Obbiwan22/Projet-cockpit_G1000_Baron_58/img/Droite.jpg

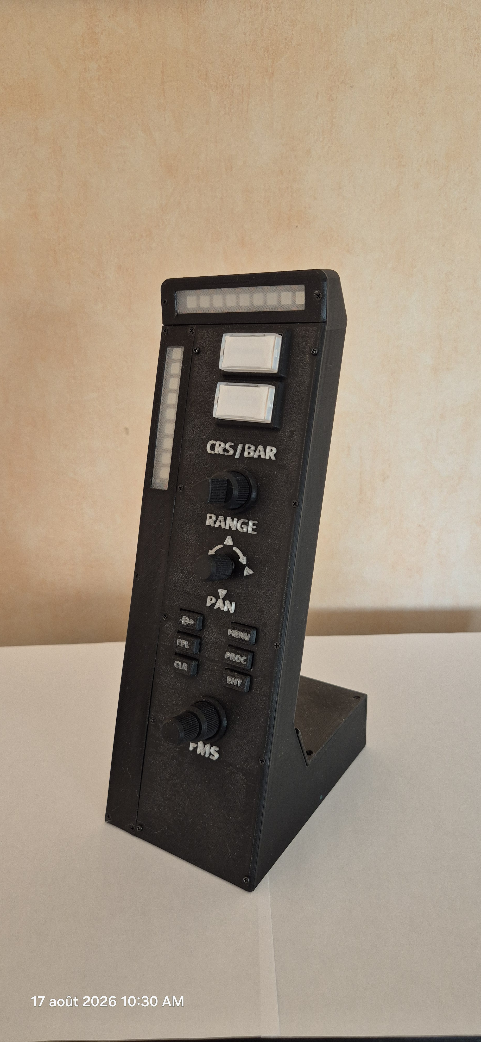
img/Droite.jpg
