Obbiwan22/Projet-cockpit_G1000_Baron_58/img/Platine Bouton sound Arriere.png

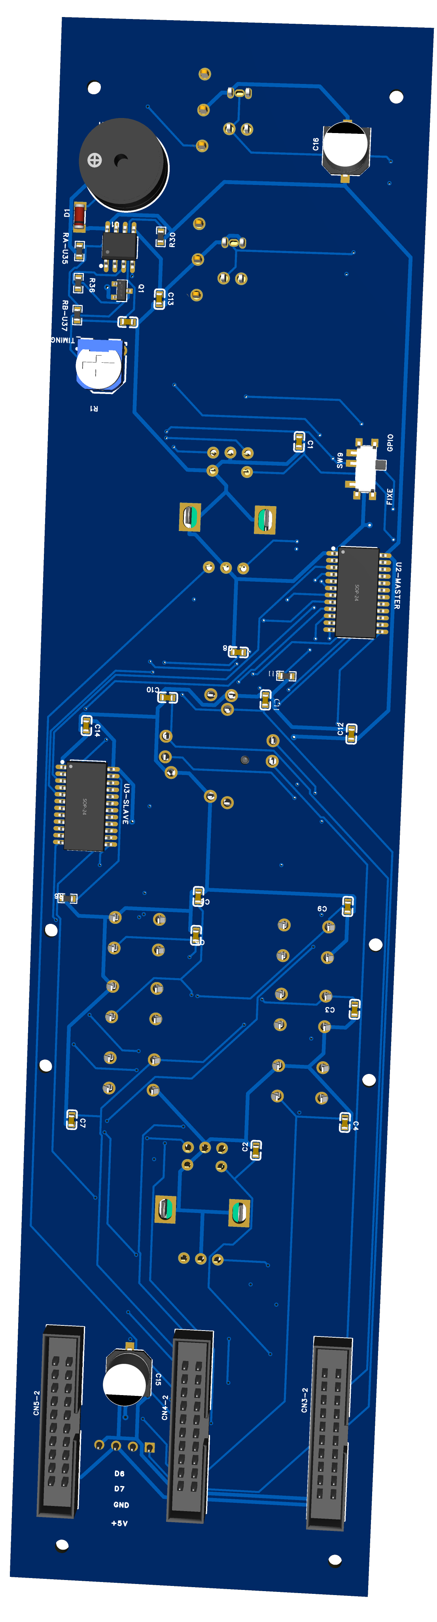
img/Platine Bouton sound Arriere.png
