Obbiwan22/Projet-cockpit_G1000_Baron_58/3D-Printing/plaque avant V3.42.STL

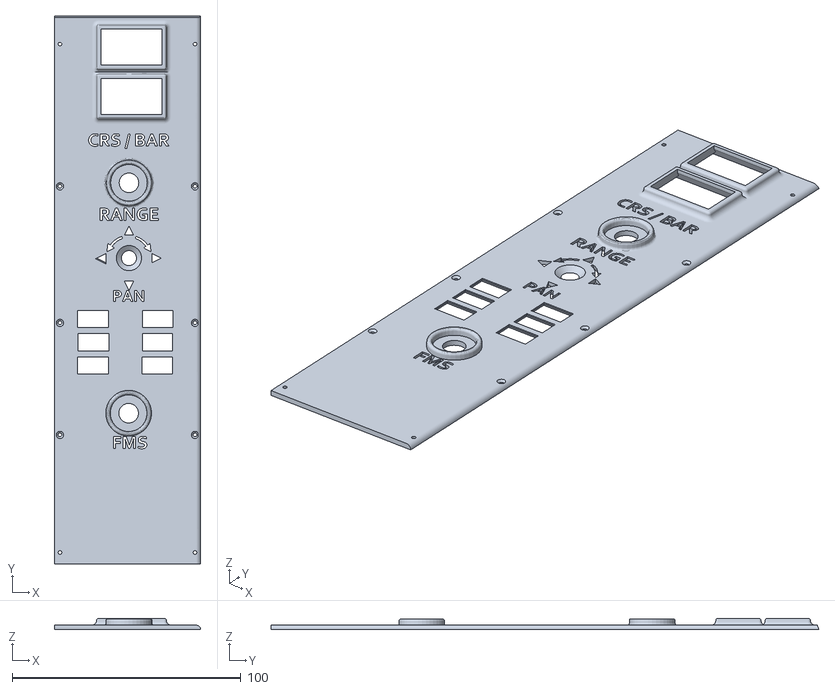
[picture p23: CAD file, 2026-08-17]
3D-Printing/plaque avant V3.42.STL
64.0 x 239.4 x 5.00
