Obbiwan22/Projet-cockpit_G1000_Baron_58/3D-Printing/plaque avant lettre V3.2.STL

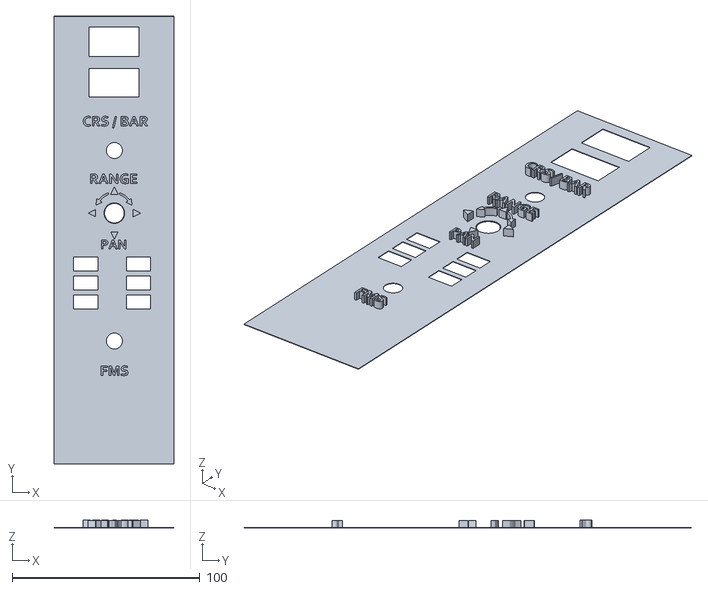
[picture p24: CAD file, 2026-08-17]
3D-Printing/plaque avant lettre V3.2.STL
64.0 x 238.8 x 4.25
