Obbiwan22/Projet-cockpit_G1000_Baron_58/firmware/ILS_NeoPixel_mega/MFCustomDevice.h

#pragma once

#include <Arduino.h>
#include "ILS_NeoPixel_mega.h"

// only one entry required if you have only one custom device
enum {
    MY_CUSTOM_DEVICE_1 = 1,
    MY_CUSTOM_DEVICE_2
};
class MFCustomDevice
{
public:
    MFCustomDevice();
    void attach(uint16_t adrPin, uint16_t adrType, uint16_t adrConfig, bool configFromFlash = false);
    void detach();
    void update();
    void set(int16_t messageID, char *setPoint);

private:
    bool           getStringFromMem(uint16_t addreeprom, char *buffer, bool configFromFlash);
    bool           _initialized = false;
    ILS_NeoPixel_mega *_mydevice;
    uint8_t        _pin1, _pin2, _pin3;
    uint8_t        _customType = 0;
};
